EddyAghaie/Esp32Gifplayer-on-1.8-inch-display/images/0.jpg

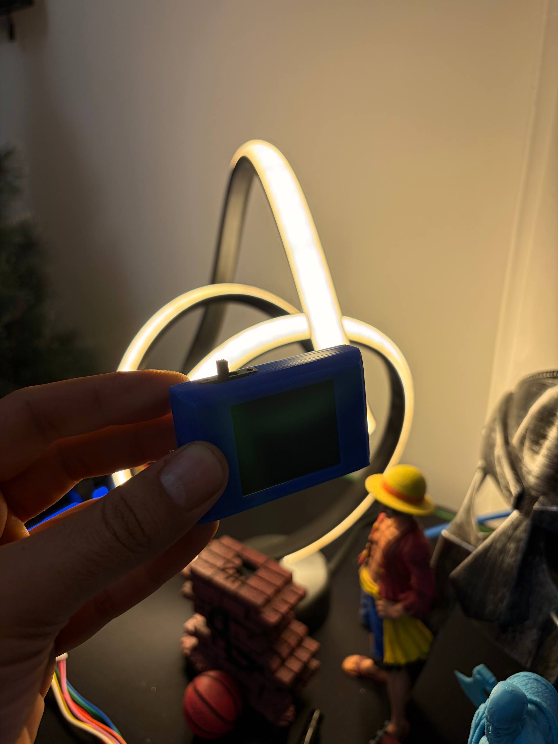
images/0.jpg
